alexanderjg85/simple_attiny13a_devboard/Firmware/Simple_Attiny_MicroOs/Simple_Attiny_MicroOs/main.h

/*
 * main.h
 *
 * Created: 31.07.2026 22:15:22
 *  Author: alexa
 */ 


#ifndef MAIN_H_
#define MAIN_H_

#include <avr/io.h>

#define F_CPU 4800000UL  ///< 4,8 Mhz internal CLK, DIV 8 not set

#define LED_BOARD PORTB4	///< Port Definition of OnBoard LED Pin


#endif /* MAIN_H_ */
