alexanderjg85/simple_attiny13a_devboard/Firmware/Simple_Attiny_MicroOs/Simple_Attiny_MicroOs/custom_types.h

/*
 * custom_types.h
 *
 * Created: 03.08.2026 20:57:30
 *  Author: alexa
 */ 


#ifndef CUSTOM_TYPES_H_
#define CUSTOM_TYPES_H_

typedef uint8_t uint8;
typedef uint16_t uint16;
typedef uint32_t uint32;
typedef int8_t sint8;
typedef int16_t sint16;
typedef int32_t sint32;



#endif /* CUSTOM_TYPES_H_ */
